microdimmer/homeweather_esp8266/graphics.h

//30 px font "48-58"
const uint8_t custom_font30[348] U8G2_FONT_SECTION("custom_font30") =
  "\13\0\4\5\5\5\5\5\6\22\37\0\0\37\367\37\0\0\0\0\0\1C\60$\362CX\303\37\4\231"
  "\36*\267\30S\15\21\221\14!\211\20\223\4AM\61\266\234\202I\246\313\17>x\0\61\21\347gX"
  "K\271\330,(\201\206!\244\374\377\17\62$\362CX\3Q\5\21t\14\61\211\20\262\4\21Q\246e"
  "\321\345\372\203\17&'\227\351\362\3\42 y\246\0\63 \362CXCB\317@\22\305\226iYty"
  "\324\24c\313)\17H\321\245N\62]~\360\301\3\64>\362CX\3a\305\20V\14a\305\20V\14"
  "a\305\20V\14a\305\20V\14a\305\20V\14a\305\20V\14a\305\20V\14a\305\20V\14a\305"
  "\20V\14A\316<\2E\243E\227\277\1\0\65\35\362CXCB\317@\22\305\226\351\234\314?\370\200"
  "\353\262N\62]Z\1\311\63\16\1\66\32\362CXCB\317@\22\305\226\351\234\34\271\346\21(\242L"
  "\371\301\7\17\67\30\362CX\3Q\15\71\363\10\24Q\246e\321\345\215;\42\234\374\237\3\70\30\362"
  "CXCB\317@\22\305\226\351/\213qGD\246\277\374\340\203\7\71\32\362CX\303\37\4\231~\371"
  "\201\25\220<StY'\231^D\2\315C\12:\11\304A|\2\365@P\0\0\0";

//8x14px font codes "28-31,43,46,48-58"
const uint8_t custom_font_14[253] U8G2_FONT_SECTION("custom_font_14") =
  "\21\0\3\5\4\4\4\4\5\10\16\0\0\17\375\17\1\0\0\0\0\0\344\34\14\226\251Z\302\210\30\22"
  "(\236\0\35\14\226\251Z\2\305\223\21b\202\0\36\16\350\210zB\211\31A&X\374\33\0\37\16\350"
  "\210z\202\305\277!\61FT\30\0+\14f\310X\2\5\61\22(\10\0.\6\42\210\24\4\60\21\350"
  "\210\32\22\311V\310\210\20C\305\10\22\224\0\61\13\343\214:B\20\5\21\377\0\62\16\350\210\32\22\11"
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
  0x83, 0xB1, 0x83, 0x91, 0xC3, 0xE1, 0xE3, 0xC1, 0x3E, 0xAF, 0x1C, 0xEE
};

static const uint8_t p_bitmap[] U8X8_PROGMEM = { // 9x14
  0x63, 0xC4, 0xC6, 0xDC, 0x8C, 0xC5, 0x08, 0xFD, 0x8C, 0xC5, 0xC6, 0xDC,
  0x63, 0xC4, 0x21, 0xFC, 0x6B, 0xC5, 0xCE, 0xDD, 0x8C, 0xC5, 0xEF, 0xFD
};
